Professor-plum/BSides-SLC-Badge-2019/img/arcade.bmp

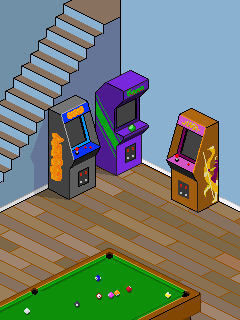
img/arcade.bmp
