Professor-plum/BSides-SLC-Badge-2019/eagle/top.png

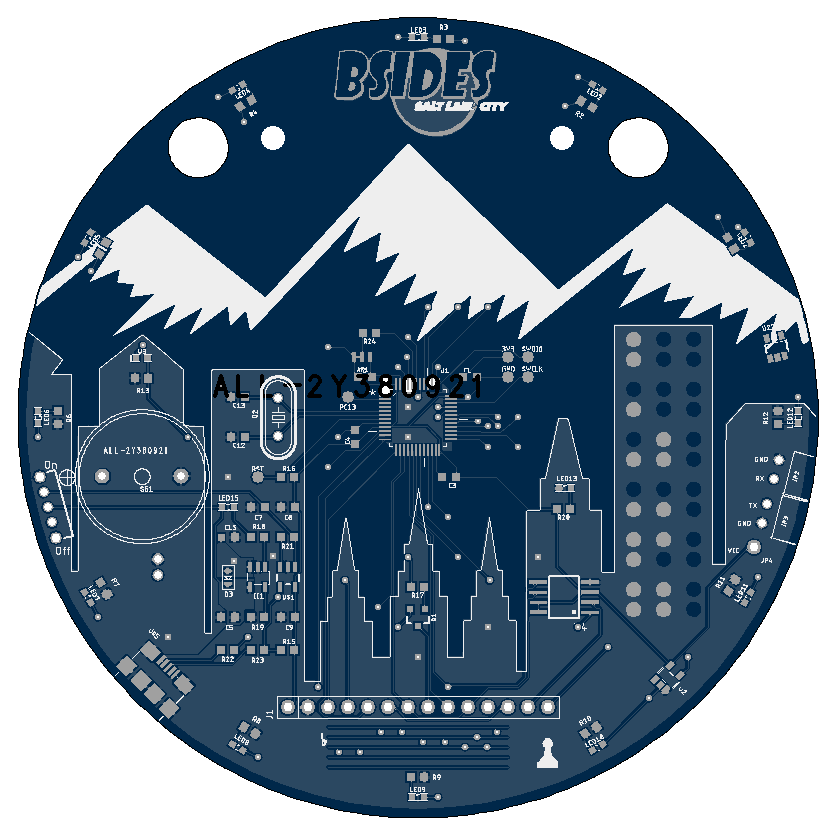
eagle/top.png
