Professor-plum/BSides-SLC-Badge-2019/gifs/Alley.gif

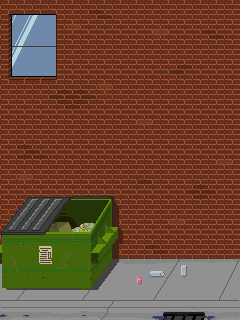
gifs/Alley.gif
