Professor-plum/BSides-SLC-Badge-2019/gifs/comp.gif

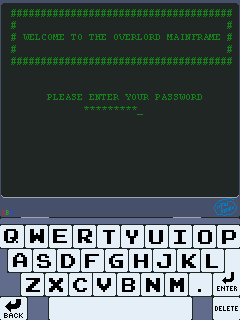
gifs/comp.gif
