Professor-plum/BSides-SLC-Badge-2019/gifs/control.gif

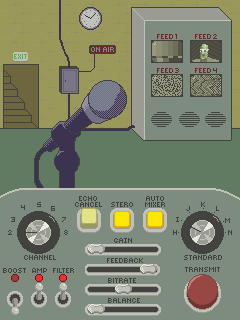
gifs/control.gif
