Professor-plum/BSides-SLC-Badge-2019/gifs/dial.gif

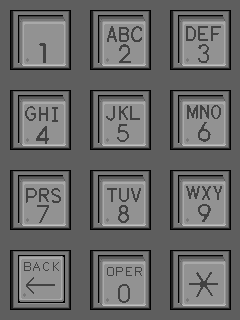
gifs/dial.gif
