Professor-plum/BSides-SLC-Badge-2019/gifs/dj.gif

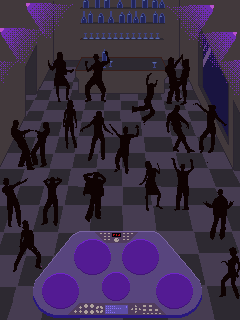
gifs/dj.gif
