Professor-plum/BSides-SLC-Badge-2019/gifs/market.gif

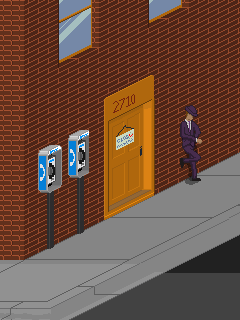
gifs/market.gif
