Professor-plum/BSides-SLC-Badge-2019/gifs/nclub2.gif

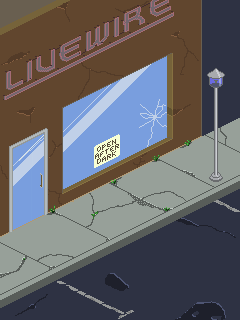
gifs/nclub2.gif
