Professor-plum/BSides-SLC-Badge-2019/gifs/puzzle.gif

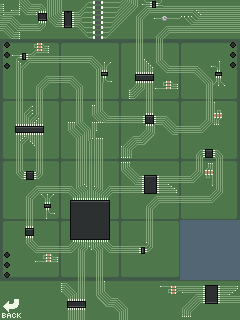
gifs/puzzle.gif
