Professor-plum/BSides-SLC-Badge-2019/gifs/street.gif

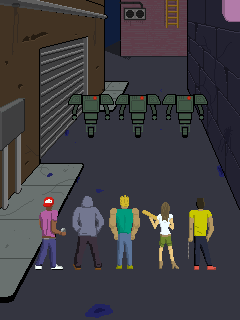
gifs/street.gif
