Professor-plum/BSides-SLC-Badge-2019/gifs/tower.gif

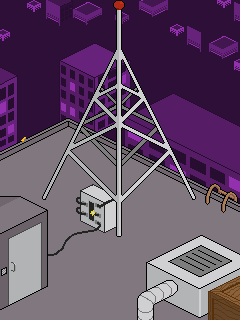
gifs/tower.gif
