Professor-plum/BSides-SLC-Badge-2019/gifs/tv.gif

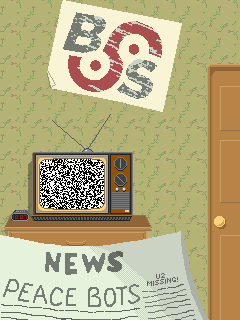
gifs/tv.gif
