Professor-plum/BSides-SLC-Badge-2019/img/comp.bmp

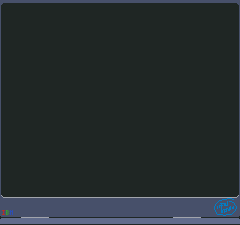
img/comp.bmp
