Professor-plum/BSides-SLC-Badge-2019/img/computer.bmp

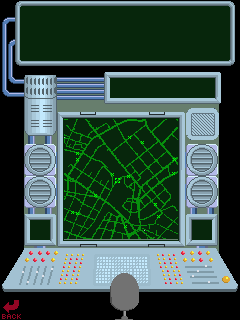
img/computer.bmp
