Professor-plum/BSides-SLC-Badge-2019/img/dj1.bmp

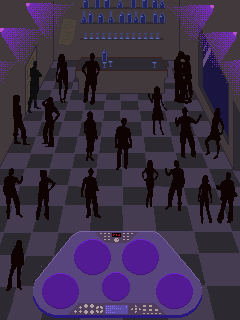
img/dj1.bmp
