Professor-plum/BSides-SLC-Badge-2019/img/dj2.bmp

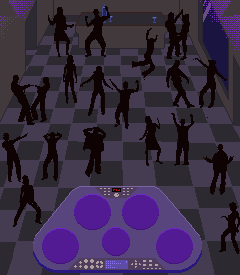
img/dj2.bmp
