Professor-plum/BSides-SLC-Badge-2019/img/dj3.bmp

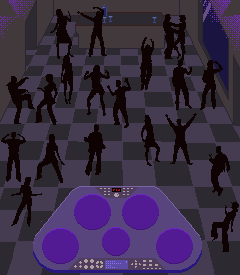
img/dj3.bmp
