Professor-plum/BSides-SLC-Badge-2019/img/street2.bmp

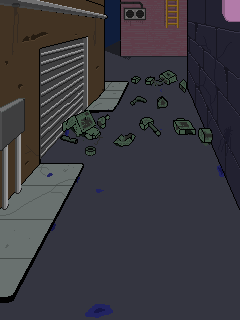
img/street2.bmp
