Professor-plum/BSides-SLC-Badge-2019/img/tv.bmp

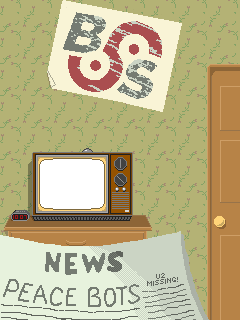
img/tv.bmp
