Professor-plum/BSides-SLC-Badge-2019/src/BsidesSLCBig/NES.h

#ifndef NES
#define NES
const uint8_t Pixel_NES5pt7bBitmaps[] PROGMEM = {
  0x0C, 0x71, 0x8C, 0x20, 0x08, 0x00, 0xB4, 0x57, 0xD5, 0xF5, 0x00, 0x10,
  0xFB, 0x43, 0xE1, 0x6F, 0x84, 0x00, 0xC7, 0x9C, 0x71, 0xC7, 0x1C, 0xF1,
  0x80, 0x73, 0x2E, 0x9D, 0xDF, 0x27, 0xC0, 0xC0, 0x7F, 0x0C, 0x30, 0xC3,
  0x07, 0xC0, 0xF8, 0x30, 0xC3, 0x0C, 0x3F, 0x80, 0x8A, 0xBE, 0xA8, 0x80,
  0x21, 0x3E, 0x42, 0x00, 0xC0, 0xF8, 0x80, 0x06, 0x1C, 0x71, 0xC7, 0x1C,
  0x30, 0x00, 0x38, 0x9B, 0x1E, 0x3C, 0x6C, 0x8E, 0x00, 0x33, 0x8C, 0x63,
  0x1B, 0xE0, 0x7D, 0x8C, 0x19, 0xE7, 0x1C, 0x3F, 0x80, 0x7E, 0x18, 0x61,
  0xE0, 0x78, 0xDF, 0x00, 0x1C, 0x79, 0xB6, 0x6F, 0xE1, 0x83, 0x00, 0xFD,
  0x83, 0xF0, 0x30, 0x78, 0xDF, 0x00, 0x3C, 0xC3, 0x07, 0xEC, 0x78, 0xDF,
  0x00, 0xFF, 0x0C, 0x30, 0xC3, 0x06, 0x0C, 0x00, 0x79, 0x8B, 0x93, 0xC9,
  0xF0, 0xDF, 0x00, 0x7D, 0x8F, 0x1B, 0xF0, 0x61, 0x9E, 0x00, 0x90, 0x98,
  0x1C, 0xCE, 0x0C, 0x1C, 0xF8, 0x3E, 0xE0, 0xC1, 0xCC, 0xE0, 0x7D, 0x8C,
  0x18, 0xE3, 0x00, 0x08, 0x00, 0x7D, 0x8F, 0x5E, 0xBD, 0xD8, 0x1F, 0x00,
  0x38, 0xDB, 0x1E, 0x3F, 0xF8, 0xF1, 0x80, 0xFD, 0x8F, 0x1F, 0xEC, 0x78,
  0xFF, 0x00, 0x3C, 0xCF, 0x06, 0x0C, 0x0C, 0xCF, 0x00, 0xF9, 0x9B, 0x1E,
  0x3C, 0x79, 0xBE, 0x00, 0xFF, 0x0C, 0x3F, 0xC3, 0x0F, 0xC0, 0xFF, 0x0C,
  0x3F, 0xC3, 0x0C, 0x00, 0x3E, 0xC3, 0x06, 0x7C, 0x6C, 0xCF, 0x80, 0xC7,
  0x8F, 0x1F, 0xFC, 0x78, 0xF1, 0x80, 0xF9, 0x8C, 0x63, 0x1B, 0xE0, 0x06,
  0x0C, 0x18, 0x30, 0x78, 0xDF, 0x00, 0xC7, 0x9B, 0x67, 0x8F, 0x9B, 0xB3,
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
  {   190,   6,   7,   7,    0,   -6 },   // 0x46 'F'
  {   196,   7,   7,   8,    0,   -6 },   // 0x47 'G'
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

const GFXfont Pixel_NES5pt7b PROGMEM = {
  (uint8_t  *)Pixel_NES5pt7bBitmaps,
  (GFXglyph *)Pixel_NES5pt7bGlyphs,
  0x20, 0x7E, 11 };

// Approx. 1213 bytes
#endif
